Jougheaux/JPEG/v0.4/STLs/Body/Lower.stl

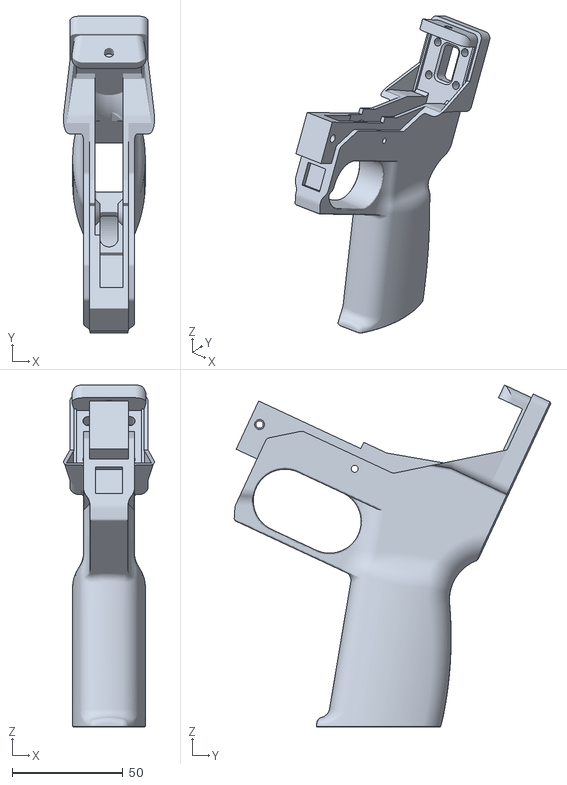
[picture p18: CAD file, 2023-08-13]
v0.4/STLs/Body/Lower.stl
41.2 x 143.2 x 154.7
