Jougheaux/JPEG/v0.4/STLs/Cage/CageBody.stl

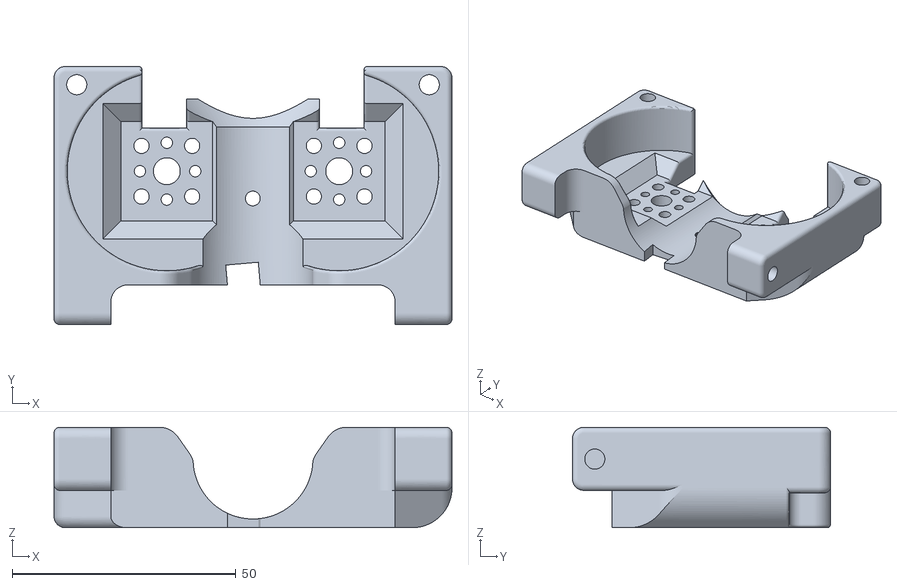
[picture p19: CAD file, 2023-08-13]
v0.4/STLs/Cage/CageBody.stl
88.9 x 57.7 x 22.4
