Jougheaux/JPEG/v0.4/STLs/Pusher/MotorHousing.stl

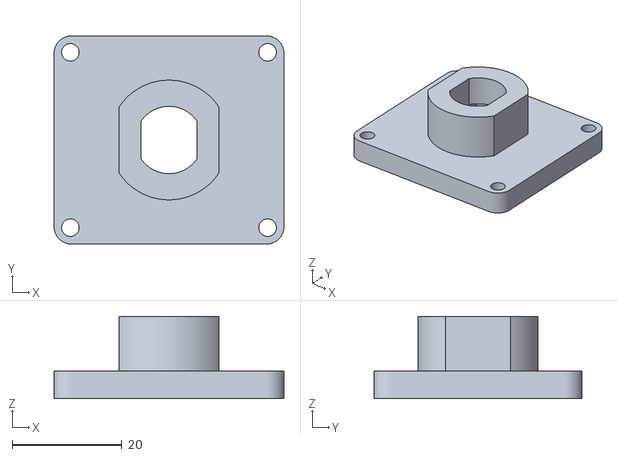
[picture p20: CAD file, 2023-11-08]
v0.4/STLs/Pusher/MotorHousing.stl
42.0 x 38.0 x 15.0
