Jougheaux/JPEG/v0.4/STLs/Stock/WorkerBatteryStock/StockBaseWorker.stl

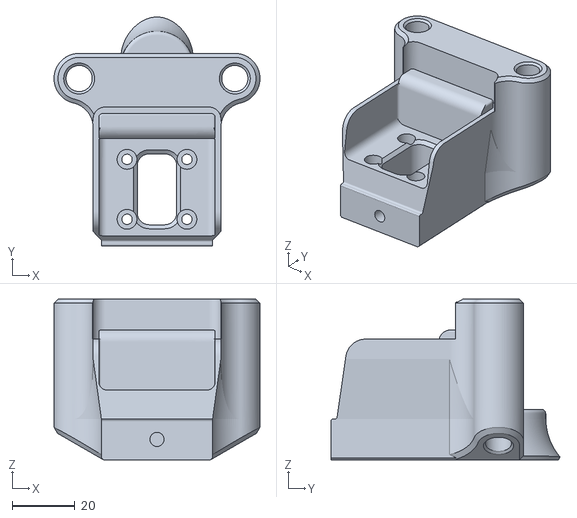
[picture p21: CAD file, 2023-08-13]
v0.4/STLs/Stock/WorkerBatteryStock/StockBaseWorker.stl
65.5 x 72.8 x 51.1
