Jougheaux/JPEG/v0.4/STLs/Accesory/BottomPicRail.stl

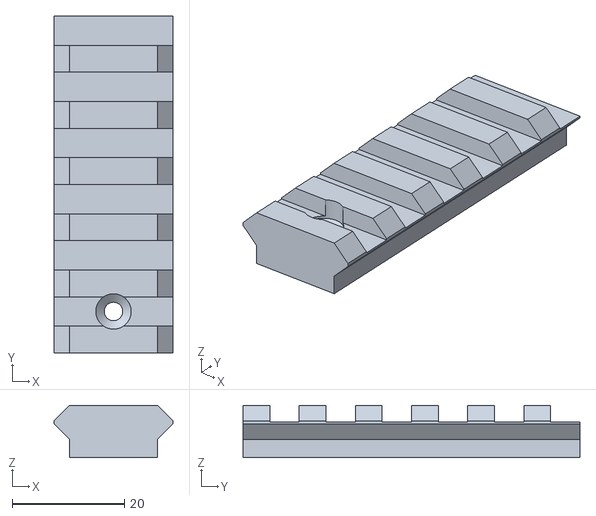
[picture p22: CAD file, 2023-06-10]
v0.4/STLs/Accesory/BottomPicRail.stl
21.2 x 60.0 x 9.32
