Jougheaux/JPEG/v0.4/STLs/Body/TopCover.stl

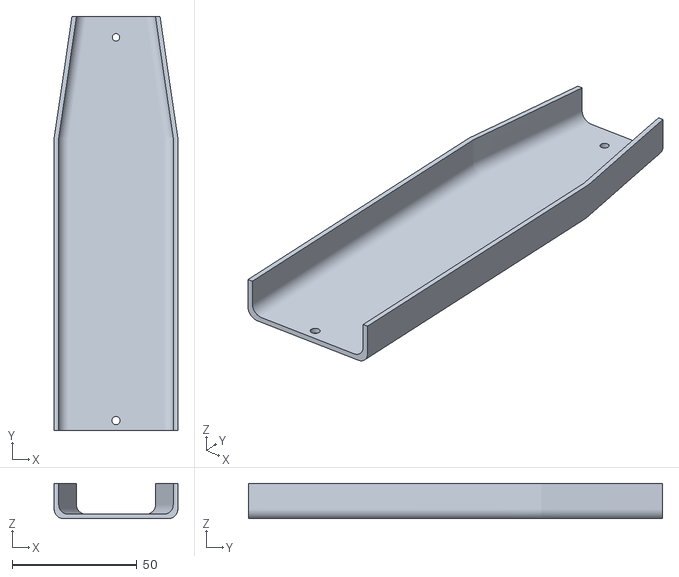
[picture p23: CAD file, 2023-06-10]
v0.4/STLs/Body/TopCover.stl
49.5 x 165.9 x 14.2
