Jougheaux/JPEG/v0.4/STLs/Cage/7mmWheelSLS.stl

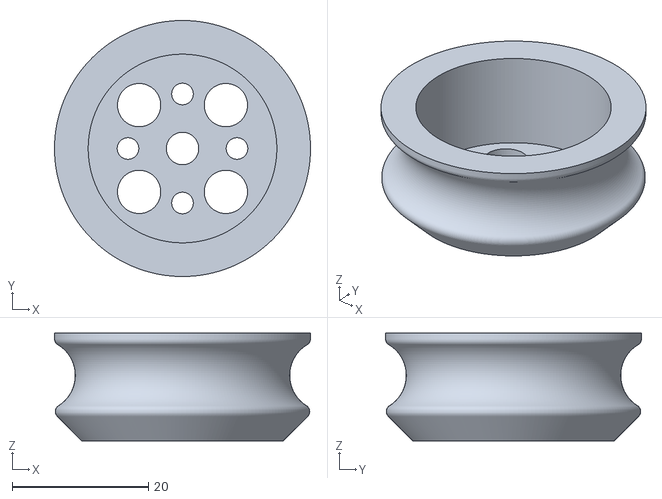
[picture p24: CAD file, 2023-08-13]
v0.4/STLs/Cage/7mmWheelSLS.stl
37.6 x 37.6 x 15.8
