Jougheaux/JPEG/v0.4/STLs/Pusher/Pusher.stl

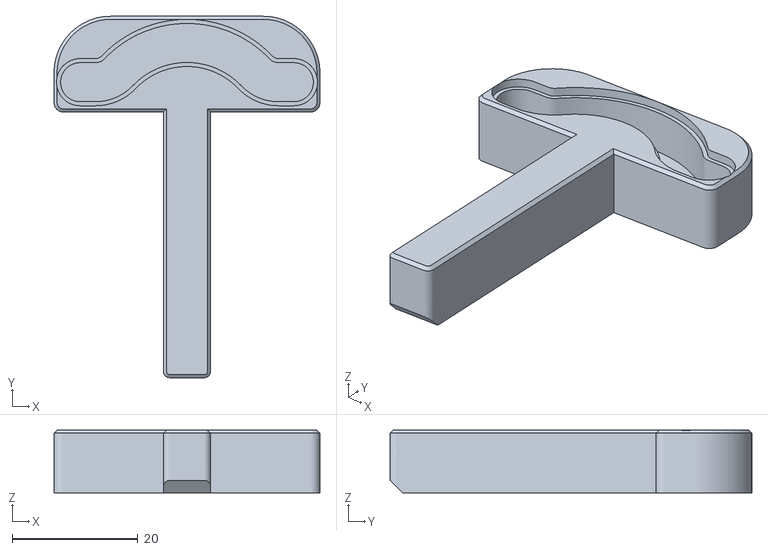
[picture p25: CAD file, 2023-11-08]
v0.4/STLs/Pusher/Pusher.stl
42.3 x 57.5 x 10.0
