Jougheaux/JPEG/v0.4/STLs/Stock/WorkerBatteryStock/StockMechPlate.stl

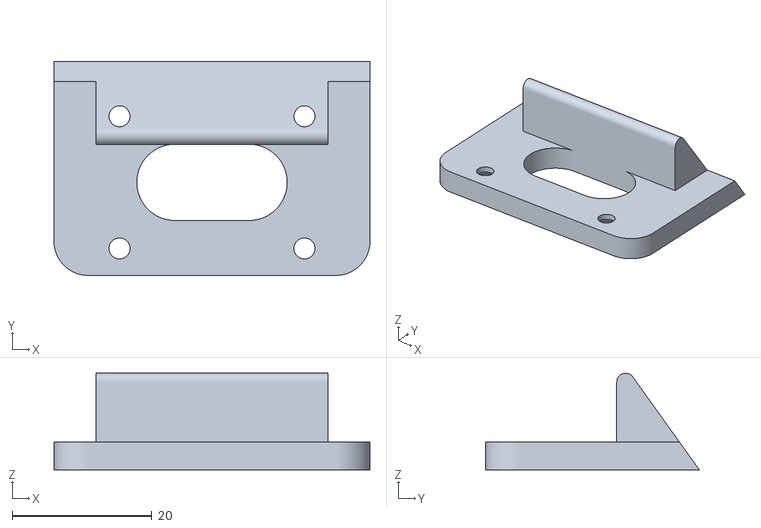
[picture p26: CAD file, 2023-07-11]
v0.4/STLs/Stock/WorkerBatteryStock/StockMechPlate.stl
45.2 x 30.6 x 13.8
