Jougheaux/JPEG/v0.4/STLs/Accesory/TopPicRail.stl

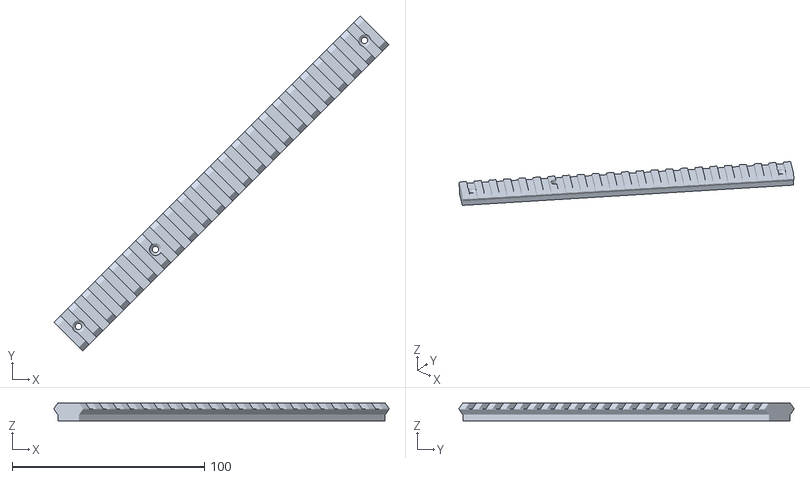
[picture p27: CAD file, 2023-06-10]
v0.4/STLs/Accesory/TopPicRail.stl
174.1 x 174.1 x 9.32
