Jougheaux/JPEG/v0.4/STLs/Cage/CageInner5deg.stl

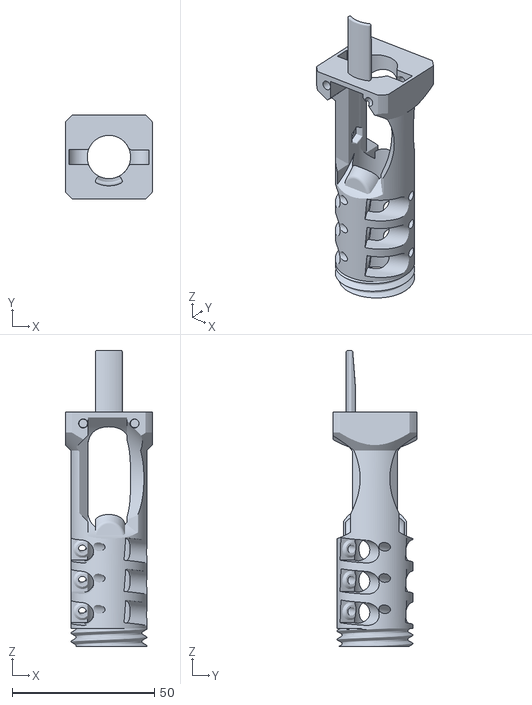
[picture p28: CAD file, 2023-08-13]
v0.4/STLs/Cage/CageInner5deg.stl
30.7 x 29.6 x 104.2
