Jougheaux/JPEG/v0.4/STLs/Accesory/Trigger.stl

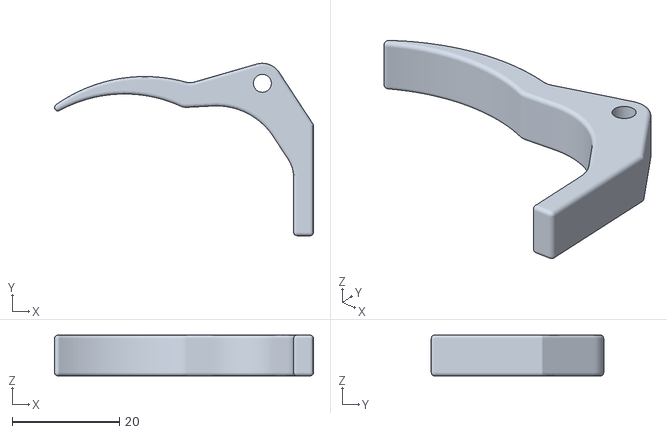
[picture p29: CAD file, 2023-06-10]
v0.4/STLs/Accesory/Trigger.stl
48.4 x 32.2 x 7.62
